stantonik/sstc-interrupter/interrupter/main/menu.h

/*
 * Copyright (C) 2025 Stanley Arnaud <stantonik@stantonik-mba.local>
 *
 * Distributed under terms of the MIT license.
 */

/**
 * @file menu.h
 * @brief 
 *
 * 
 *
 * @author Stanley Arnaud 
 * @date 09/26/2025
 * @version 0
 */

#ifndef MENU_H
#define MENU_H

// clang-format off
#ifdef __cplusplus
extern "C" 
{
#endif

// -----------------------------------------------------------------------------
// Function Declarations
// -----------------------------------------------------------------------------
void menu_init(void);

#ifdef __cplusplus
}
#endif
// clang-format on

#endif /* !MENU_H */
