stantonik/sstc-interrupter/interrupter/main/ui/screens.c

#include <string.h>

#include "screens.h"
#include "images.h"
#include "fonts.h"
#include "actions.h"
#include "vars.h"
#include "styles.h"
#include "ui.h"

static inline lv_theme_t * lv_theme_default_init(lv_disp_t * dispp,
                                                 lv_color_t color_primary,
                                                 lv_color_t color_secondary,
                                                 bool dark,
                                                 const lv_font_t * font)
{
    // Ignore parameters except the display and font
    (void)color_primary;
    (void)color_secondary;
    (void)font;

    // Call your monochrome theme initializer
    return lv_theme_mono_init(dispp, false, LV_FONT_DEFAULT);
}

#include <string.h>

objects_t objects;
lv_obj_t *tick_value_change_obj;
uint32_t active_theme_index = 0;

void create_screen_main() {
    lv_obj_t *obj = lv_obj_create(0);
    objects.main = obj;
    lv_obj_set_pos(obj, 0, 0);
    lv_obj_set_size(obj, 128, 64);
    {
        lv_obj_t *parent_obj = obj;
        {
            lv_obj_t *obj = lv_obj_create(parent_obj);
            lv_obj_set_pos(obj, 0, 0);
            lv_obj_set_size(obj, 128, 11);
            lv_obj_set_style_pad_left(obj, 0, LV_PART_MAIN | LV_STATE_DEFAULT);
            lv_obj_set_style_pad_top(obj, 0, LV_PART_MAIN | LV_STATE_DEFAULT);
            lv_obj_set_style_pad_right(obj, 0, LV_PART_MAIN | LV_STATE_DEFAULT);
            lv_obj_set_style_pad_bottom(obj, 0, LV_PART_MAIN | LV_STATE_DEFAULT);
            lv_obj_set_style_bg_opa(obj, 0, LV_PART_MAIN | LV_STATE_DEFAULT);
            lv_obj_set_style_border_width(obj, 0, LV_PART_MAIN | LV_STATE_DEFAULT);
            lv_obj_set_style_radius(obj, 0, LV_PART_MAIN | LV_STATE_DEFAULT);
            {
                lv_obj_t *parent_obj = obj;
                {
                    // spark
                    lv_obj_t *obj = lv_img_create(parent_obj);
                    objects.spark = obj;
                    lv_obj_set_pos(obj, 60, 2);
                    lv_obj_set_size(obj, LV_SIZE_CONTENT, LV_SIZE_CONTENT);
                    lv_img_set_src(obj, &img_spark);
                    lv_obj_set_style_pad_right(obj, 2, LV_PART_MAIN | LV_STATE_DEFAULT);
                    lv_obj_set_style_pad_left(obj, 2, LV_PART_MAIN | LV_STATE_DEFAULT);
                }
                {
                    // con_state
                    lv_obj_t *obj = lv_label_create(parent_obj);
                    objects.con_state = obj;
                    lv_obj_set_pos(obj, 10, 0);
                    lv_obj_set_size(obj, LV_SIZE_CONTENT, LV_SIZE_CONTENT);
                    lv_obj_set_style_text_font(obj, &lv_font_montserrat_10, LV_PART_MAIN | LV_STATE_DEFAULT);
                    lv_label_set_text(obj, "USB");
                }
                {
                    // note
                    lv_obj_t *obj = lv_img_create(parent_obj);
                    objects.note = obj;
                    lv_obj_set_pos(obj, 0, 2);
                    lv_obj_set_size(obj, LV_SIZE_CONTENT, LV_SIZE_CONTENT);
                    lv_img_set_src(obj, &img_note);
                    lv_obj_set_style_pad_left(obj, 2, LV_PART_MAIN | LV_STATE_DEFAULT);
                    lv_obj_set_style_pad_right(obj, 2, LV_PART_MAIN | LV_STATE_DEFAULT);
                }
                {
                    // state
                    lv_obj_t *obj = lv_label_create(parent_obj);
                    objects.state = obj;
                    lv_obj_set_pos(obj, 102, 0);
                    lv_obj_set_size(obj, LV_SIZE_CONTENT, LV_SIZE_CONTENT);
                    lv_obj_set_style_text_font(obj, &lv_font_montserrat_10, LV_PART_MAIN | LV_STATE_DEFAULT);
                    lv_obj_set_style_text_align(obj, LV_TEXT_ALIGN_RIGHT, LV_PART_MAIN | LV_STATE_DEFAULT);
                    lv_obj_set_style_pad_right(obj, 2, LV_PART_MAIN | LV_STATE_DEFAULT);
                    lv_label_set_text(obj, "IDLE");
                }
            }
        }
        {
            lv_obj_t *obj = lv_obj_create(parent_obj);
            lv_obj_set_pos(obj, 0, 11);
            lv_obj_set_size(obj, 128, 53);
            lv_obj_set_style_pad_left(obj, 0, LV_PART_MAIN | LV_STATE_DEFAULT);
            lv_obj_set_style_pad_top(obj, 0, LV_PART_MAIN | LV_STATE_DEFAULT);
            lv_obj_set_style_pad_right(obj, 0, LV_PART_MAIN | LV_STATE_DEFAULT);
            lv_obj_set_style_pad_bottom(obj, 0, LV_PART_MAIN | LV_STATE_DEFAULT);
            lv_obj_set_style_bg_opa(obj, 0, LV_PART_MAIN | LV_STATE_DEFAULT);
            lv_obj_set_style_border_width(obj, 0, LV_PART_MAIN | LV_STATE_DEFAULT);
            lv_obj_set_style_radius(obj, 0, LV_PART_MAIN | LV_STATE_DEFAULT);
            {
                lv_obj_t *parent_obj = obj;
                {
                    // prf_range
                    lv_obj_t *obj = lv_obj_create(parent_obj);
                    objects.prf_range = obj;
                    lv_obj_set_pos(obj, 65, 0);
                    lv_obj_set_size(obj, 63, 53);
                    lv_obj_set_style_pad_left(obj, 0, LV_PART_MAIN | LV_STATE_DEFAULT);
                    lv_obj_set_style_pad_top(obj, 0, LV_PART_MAIN | LV_STATE_DEFAULT);
                    lv_obj_set_style_pad_right(obj, 0, LV_PART_MAIN | LV_STATE_DEFAULT);
                    lv_obj_set_style_pad_bottom(obj, 0, LV_PART_MAIN | LV_STATE_DEFAULT);
                    lv_obj_set_style_bg_opa(obj, 0, LV_PART_MAIN | LV_STATE_DEFAULT);
                    lv_obj_set_style_border_width(obj, 0, LV_PART_MAIN | LV_STATE_DEFAULT);
                    lv_obj_set_style_radius(obj, 0, LV_PART_MAIN | LV_STATE_DEFAULT);
                    {
                        lv_obj_t *parent_obj = obj;
                        {
                            // prf_txt
                            lv_obj_t *obj = lv_label_create(parent_obj);
                            objects.prf_txt = obj;
                            lv_obj_set_pos(obj, 0, 13);
                            lv_obj_set_size(obj, LV_PCT(100), LV_SIZE_CONTENT);
                            lv_obj_set_style_text_align(obj, LV_TEXT_ALIGN_CENTER, LV_PART_MAIN | LV_STATE_DEFAULT);
                            lv_label_set_text(obj, "PRF");
                        }
                        {
                            // prf_val_txt
                            lv_obj_t *obj = lv_label_create(parent_obj);
                            objects.prf_val_txt = obj;
                            lv_obj_set_pos(obj, 14, 29);
                            lv_obj_set_size(obj, 36, LV_SIZE_CONTENT);
                            lv_obj_set_style_text_align(obj, LV_TEXT_ALIGN_CENTER, LV_PART_MAIN | LV_STATE_DEFAULT);
                            lv_label_set_text(obj, "0");
                        }
                    }
                }
                {
                    // dc_range
                    lv_obj_t *obj = lv_obj_create(parent_obj);
                    objects.dc_range = obj;
                    lv_obj_set_pos(obj, 0, 0);
                    lv_obj_set_size(obj, 63, 53);
                    lv_obj_set_style_pad_left(obj, 0, LV_PART_MAIN | LV_STATE_DEFAULT);
                    lv_obj_set_style_pad_top(obj, 0, LV_PART_MAIN | LV_STATE_DEFAULT);
                    lv_obj_set_style_pad_right(obj, 0, LV_PART_MAIN | LV_STATE_DEFAULT);
                    lv_obj_set_style_pad_bottom(obj, 0, LV_PART_MAIN | LV_STATE_DEFAULT);
                    lv_obj_set_style_bg_opa(obj, 0, LV_PART_MAIN | LV_STATE_DEFAULT);
                    lv_obj_set_style_border_width(obj, 0, LV_PART_MAIN | LV_STATE_DEFAULT);
                    lv_obj_set_style_radius(obj, 0, LV_PART_MAIN | LV_STATE_DEFAULT);
                    {
                        lv_obj_t *parent_obj = obj;
                        {
                            // dc_txt
                            lv_obj_t *obj = lv_label_create(parent_obj);
                            objects.dc_txt = obj;
                            lv_obj_set_pos(obj, 0, 13);
                            lv_obj_set_size(obj, LV_PCT(100), LV_SIZE_CONTENT);
                            lv_obj_set_style_text_align(obj, LV_TEXT_ALIGN_CENTER, LV_PART_MAIN | LV_STATE_DEFAULT);
                            lv_label_set_text(obj, ">DC<");
                        }
                        {
                            // dc_val_txt
                            lv_obj_t *obj = lv_label_create(parent_obj);
                            objects.dc_val_txt = obj;
                            lv_obj_set_pos(obj, 14, 29);
                            lv_obj_set_size(obj, 36, LV_SIZE_CONTENT);
                            lv_obj_set_style_text_align(obj, LV_TEXT_ALIGN_CENTER, LV_PART_MAIN | LV_STATE_DEFAULT);
                            lv_label_set_text(obj, "0");
                        }
                    }
                }
            }
        }
    }
    
    tick_screen_main();
}

void tick_screen_main() {
}



typedef void (*tick_screen_func_t)();
tick_screen_func_t tick_screen_funcs[] = {
    tick_screen_main,
};
void tick_screen(int screen_index) {
    tick_screen_funcs[screen_index]();
}
void tick_screen_by_id(enum ScreensEnum screenId) {
    tick_screen_funcs[screenId - 1]();
}

void create_screens() {
    lv_disp_t *dispp = lv_disp_get_default();
    lv_theme_t *theme = lv_theme_default_init(dispp, lv_palette_main(LV_PALETTE_BLUE), lv_palette_main(LV_PALETTE_RED), true, LV_FONT_DEFAULT);
    lv_disp_set_theme(dispp, theme);
    
    create_screen_main();
}
