stantonik/sstc-interrupter/interrupter/main/ui/ui_image_note.c

#ifdef __has_include
    #if __has_include("lvgl.h")
        #ifndef LV_LVGL_H_INCLUDE_SIMPLE
            #define LV_LVGL_H_INCLUDE_SIMPLE
        #endif
    #endif
#endif
#ifdef __has_include
    #if __has_include("lvgl.h")
        #ifndef LV_LVGL_H_INCLUDE_SIMPLE
            #define LV_LVGL_H_INCLUDE_SIMPLE
        #endif
    #endif
#endif

#if defined(LV_LVGL_H_INCLUDE_SIMPLE)
    #include "lvgl.h"
#else
    #include "lvgl/lvgl.h"
#endif


#ifndef LV_ATTRIBUTE_MEM_ALIGN
#define LV_ATTRIBUTE_MEM_ALIGN
#endif

#ifndef LV_ATTRIBUTE_IMG_IMG_NOTE
#define LV_ATTRIBUTE_IMG_IMG_NOTE
#endif

const LV_ATTRIBUTE_MEM_ALIGN LV_ATTRIBUTE_LARGE_CONST LV_ATTRIBUTE_IMG_IMG_NOTE uint8_t img_note_map[] = {
  0x1c, 
  0x7c, 
  0x64, 
  0x44, 
  0x4c, 
  0xcc, 
  0xc0, 
};

const lv_img_dsc_t img_note = {
  .header.cf = LV_IMG_CF_ALPHA_1BIT,
  .header.always_zero = 0,
  .header.reserved = 0,
  .header.w = 6,
  .header.h = 7,
  .data_size = 7,
  .data = img_note_map,
};
